amdelt42/mixed-signal-daq-pyro-controller/JST_PH_SM4_STEP_FILES/JST S2B-PH-SM4-TB.step

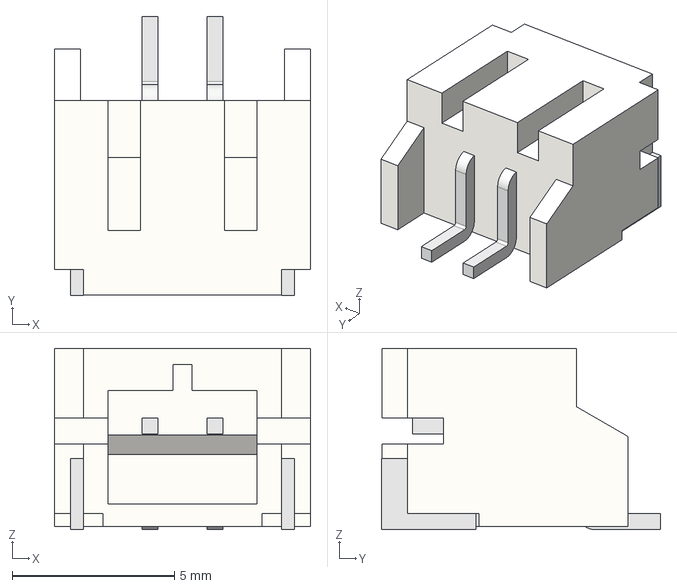
[picture p16: CAD file, 2026-08-20]
JST_PH_SM4_STEP_FILES/JST S2B-PH-SM4-TB.step
7.90 x 8.61 x 5.60 mm
