amdelt42/mixed-signal-daq-pyro-controller/GENERAL_STEP_FILES/LM27762.stp

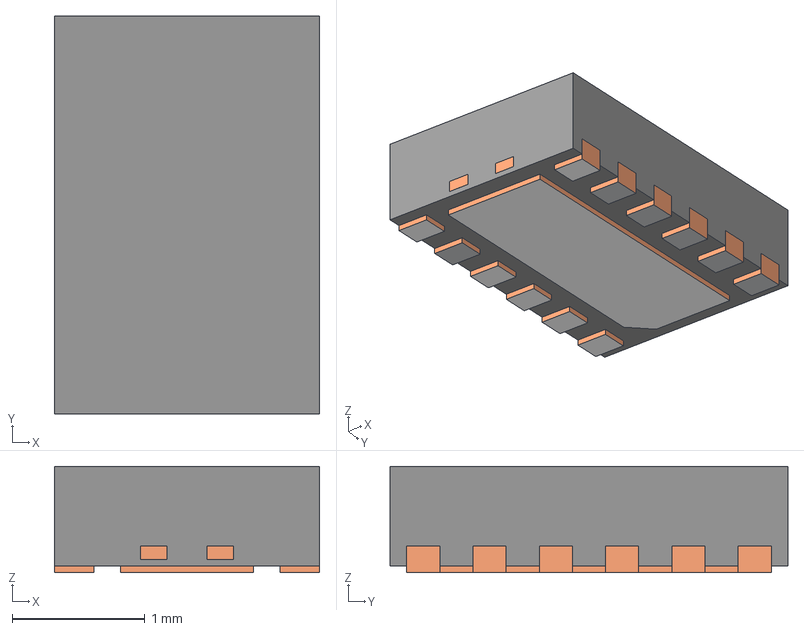
[picture p18: CAD file, 2026-08-20]
GENERAL_STEP_FILES/LM27762.stp
2.00 x 3.00 x 0.8 mm
BODY-SON
FRAME-DSS0012B
PIN1-ID
